nistur/extractor/modules/mod_exhaust.scad

/*
 * Copyright (c) 2023 Philipp Geyer
 *
 * This software is provided 'as-is', without any express or implied warranty. In no
 * event will the authors be held liable for any damages arising from the use of this
 * software.
 *
 * Permission is granted to anyone to use this software for any purpose, including
 * commercial applications, and to alter it and redistribute it freely, subject to the
 * following restrictions:
 *
 * 1. The origin of this software must not be misrepresented; you must not claim
 *    that you wrote the original software. If you use this software in a product,
 *    an acknowledgment in the product documentation would be appreciated
 *    but is not required.
 * 2. Altered source versions must be plainly marked as such, and must not be
 *    misrepresented as being the original software.
 * 3. This notice may not be removed or altered from any source distribution.
 *
 * Philipp Geyer
 * nistur@gmail.com
 */

include <../params.scad>
include <../lib/utils.scad>


d = connector_od + (connector_od - connector_id);

module ex_outer()
{
    cylinder(h=exhaust_length, r=(d/2));
}

module ex_inner()
{
    translate([0,0,-0.5])
      cylinder(h=exhaust_length+1, r=connector_od/2);
}

module ex_connector()
{
    // Create a simple connector pipe - this should be the opposite of the extractor - it should be wider than
    // the pipe's OD, and slot over the top - it should therefore also have a taper on the inside
    difference()
    {
        ex_outer();
        ex_inner();
	translate([0,0,exhaust_length-connector_taperlength])
	    cylinder(h=connector_taperlength,r1=connector_od/2, r2=(connector_od+connector_taperamount)/2);
    }
}

module ex_screw_holes()
{
    // Use the same mounting pattern as is used in the extractor enclosure. No reason to define another
    translate([ screw_separation/2,  screw_separation/2, -thickness/2]) cylinder(r=screw_diameter/2, h=thickness*2);
    translate([ screw_separation/2, -screw_separation/2, -thickness/2]) cylinder(r=screw_diameter/2, h=thickness*2);
    translate([-screw_separation/2,  screw_separation/2, -thickness/2]) cylinder(r=screw_diameter/2, h=thickness*2);
    translate([-screw_separation/2, -screw_separation/2, -thickness/2]) cylinder(r=screw_diameter/2, h=thickness*2);
}

module ex_grille()
{
    // Guess at the amount of hexes we need to fill the space
    // (this is correct in one direction, but because each row overlaps slightly
    // and I don't feel like working out the maths, this is fine for now)
    n = d / (hex_size + hex_spacing);
    intersection()
    {
	hex_grid(hex_size, hex_spacing, 1+n, n, thickness * 2);
	ex_inner();
    }
}

module ex_mount()
{
    union()
    {
	difference()
	{
	    // Base shape - same as the extractor connector, just for simplicity
	    rounded_box(base_size, base_size, thickness, corner_radius);
	    // cut out a hex grille - to keep leaves etc out I guess
	    translate([0,0,-thickness/2]) ex_grille();
	    // some mounting holes
	    ex_screw_holes();
	}
    }
}

module exhaust()
{
    // Connector, should be the opposite to that used in `connector` so that these could be
    // used together - or used with a pipe in between
    translate([0,0,thickness]) ex_connector();

    // Add the mounting plate
    ex_mount();
}
